homebrew8088/pi86/code/v30/keycodes.h

#ifndef KEYCODES_H
#define KEYCODES_H

const char scan_codes[] = {               	//Scan Codes Table 
//     0,    1,    2,    3,    4,    5,    6,    7,    8,    9,    A,    B,    C,    D,    E     F
// 				   			   A,    B,    C,    D,    E,    F,    G,    H,    I,    J,    K,    L,    
	0X00, 0X00, 0X00, 0X00, 0X1E, 0X30, 0X2E, 0X20, 0X12, 0X21, 0X22, 0X23, 0X17, 0X24, 0X25, 0X26, //0x000
//     M,    N,    O,    P,    Q,    R,    S,    T,    U,    V,    W,    X,    Y,    Z,    1     2
	0X32, 0X31, 0X18, 0X19, 0X10, 0X13, 0X1F, 0X14, 0X16, 0X2F, 0X11, 0X2D, 0X15, 0X2C, 0X02, 0X03,  //0x010
//	   3	 4	   5	 6     7     8     9     0   RET   ESC	BSK    TAB	SPC   -     =        [
	0X04, 0X05, 0X06, 0X07, 0X08, 0X09, 0X0A, 0X0B, 0X1C, 0X01, 0X0E, 0X0F, 0X39, 0X0C, 0X0D, 0X1B, //0x0020 
//    [     '\'         ;     '    ~       ,      .    /   CAP    F1    F2    F3    F4    F5    F6
	0X1A, 0X2B, 0X00, 0X27, 0X28, 0X29, 0X33, 0X34, 0X35, 0X3A, 0X3B, 0X3C, 0X3D, 0X3E, 0X3F, 0X40, //0x0030 
//     0,    1,    2,    3,    4,    5,    6,    7,    8,    9,    A,    B,    C,    D,    E     F
//	  F7   F8    F9    F10   F11   F12  PSCR  SLCK  PAUS                                        ->
	0X41, 0X42, 0X43, 0X44, 0X57, 0X58, 0X37, 0X47, 0X00, 0X00, 0X00, 0X00, 0X53, 0X00, 0X00, 0X4D, //0x0040
//	<-    DOWN    UP
	0X4B, 0X50, 0X48, 0X00, 0X00, 0X00, 0X00, 0X00, 0X00, 0X00, 0X00, 0X00, 0X00, 0X00, 0X00, 0X00, //0x0050 
	0X00, 0X00, 0X00, 0X00, 0X00, 0X00, 0X00, 0X00, 0X00, 0X00, 0X00, 0X00, 0X00, 0X00, 0X00, 0X00, //0x0060
	0X00, 0X00, 0X00, 0X00, 0X00, 0X00, 0X00, 0X00, 0X00, 0X00, 0X00, 0X00, 0X00, 0X00, 0X00, 0X00, //0x0070 
	0X00, 0X00, 0X00, 0X00, 0X00, 0X00, 0X00, 0X00, 0X00, 0X00, 0X00, 0X00, 0X00, 0X00, 0X00, 0X00, //0x0080
	0X00, 0X00, 0X00, 0X00, 0X00, 0X00, 0X00, 0X00, 0X00, 0X00, 0X00, 0X00, 0X00, 0X00, 0X00, 0X00, //0x0090 
	0X00, 0X00, 0X00, 0X00, 0X00, 0X00, 0X00, 0X00, 0X00, 0X00, 0X00, 0X00, 0X00, 0X00, 0X00, 0X00, //0x00A0
	0X00, 0X00, 0X00, 0X00, 0X00, 0X00, 0X00, 0X00, 0X00, 0X00, 0X00, 0X00, 0X00, 0X00, 0X00, 0X00, //0x00B0 
	0X00, 0X00, 0X00, 0X00, 0X00, 0X00, 0X00, 0X00, 0X00, 0X00, 0X00, 0X00, 0X00, 0X00, 0X00, 0X00, //0x00C0
	0X00, 0X00, 0X00, 0X00, 0X00, 0X00, 0X00, 0X00, 0X00, 0X00, 0X00, 0X00, 0X00, 0X00, 0X00, 0X00, //0x00D0 
//     0,    1,    2,    3,    4,    5,    6,    7,    8,    9,    A,    B,    C,    D,    E     F
//  LCTR, LSHF, LALT, LGUI, RCTR, RSHF, RALT, RGUI,    8,    9,    A,    B,    C,    D,    E     F
	0X1D, 0X2A, 0X38, 0X00, 0X1D, 0X36, 0X38, 0X00, 0X00, 0X00, 0X00, 0X00, 0X00, 0X00, 0X00, 0X00, //0x00E0
	0X00, 0X00, 0X00, 0X00, 0X00, 0X00, 0X00, 0X00, 0X00, 0X00, 0X00, 0X00, 0X00, 0X00, 0X00, 0X00, //0x00F0 
	0X00, 0X00, 0X00, 0X00, 0X00, 0X00, 0X00, 0X00, 0X00, 0X00, 0X00, 0X00, 0X00, 0X00, 0X00, 0X00, //0x0100
	0X00, 0X00, 0X00, 0X00, 0X00, 0X00, 0X00, 0X00, 0X00, 0X00, 0X00, 0X00, 0X00, 0X00, 0X00, 0X00 //0x0110
};


#endif
